Lebo77/Alarm-Clock/Photos/DSC01660.jpg

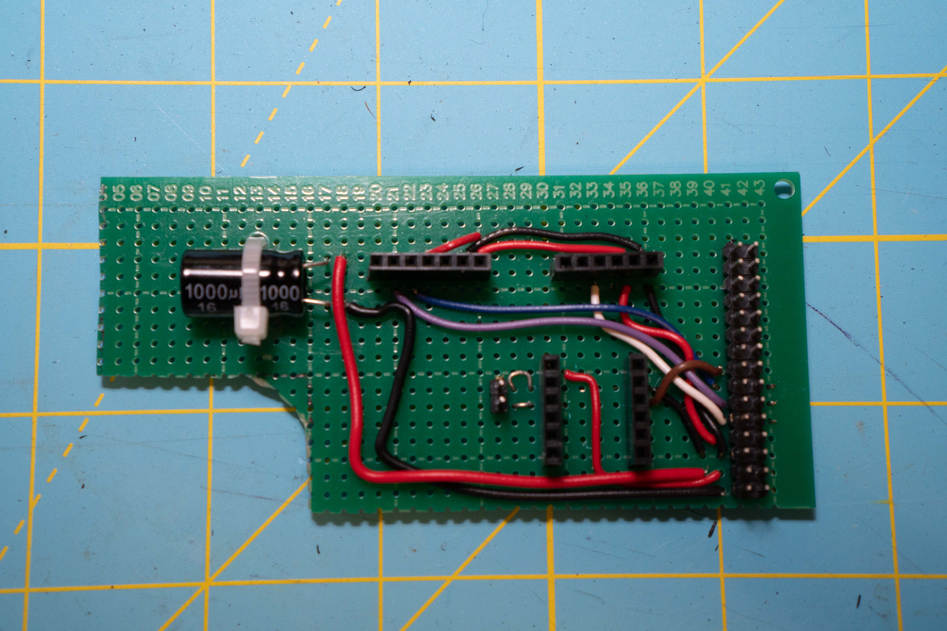
Photos/DSC01660.jpg
