Lebo77/Alarm-Clock/Photos/DSC01661.jpg

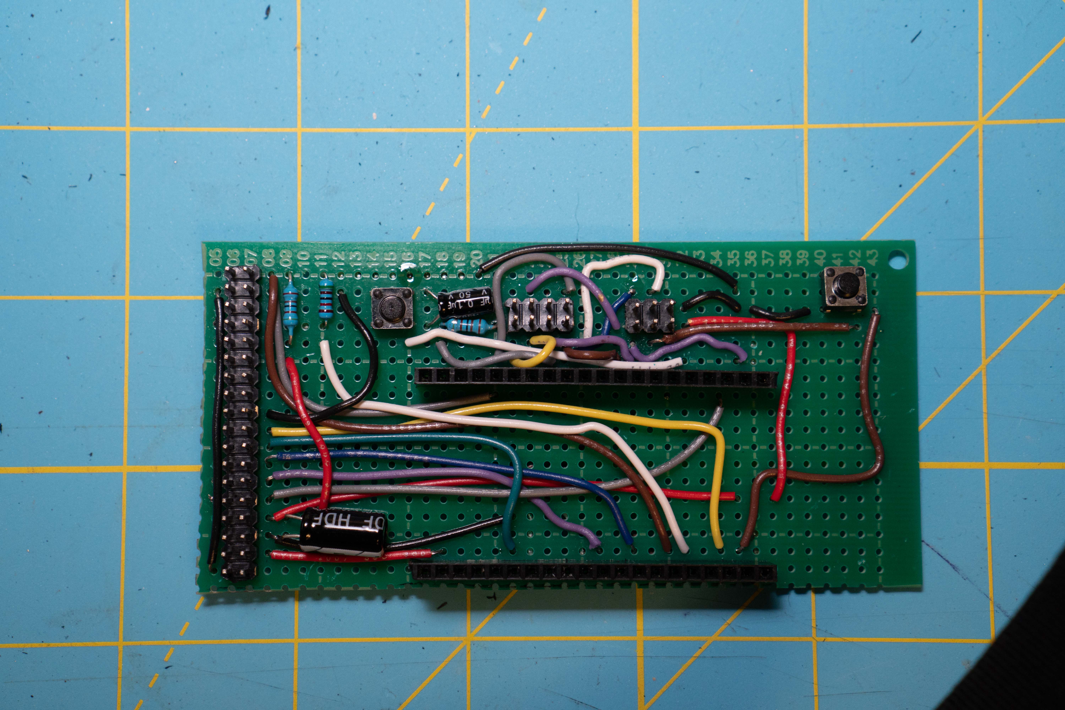
Photos/DSC01661.jpg
