Lebo77/Alarm-Clock/Photos/DSC01662.jpg

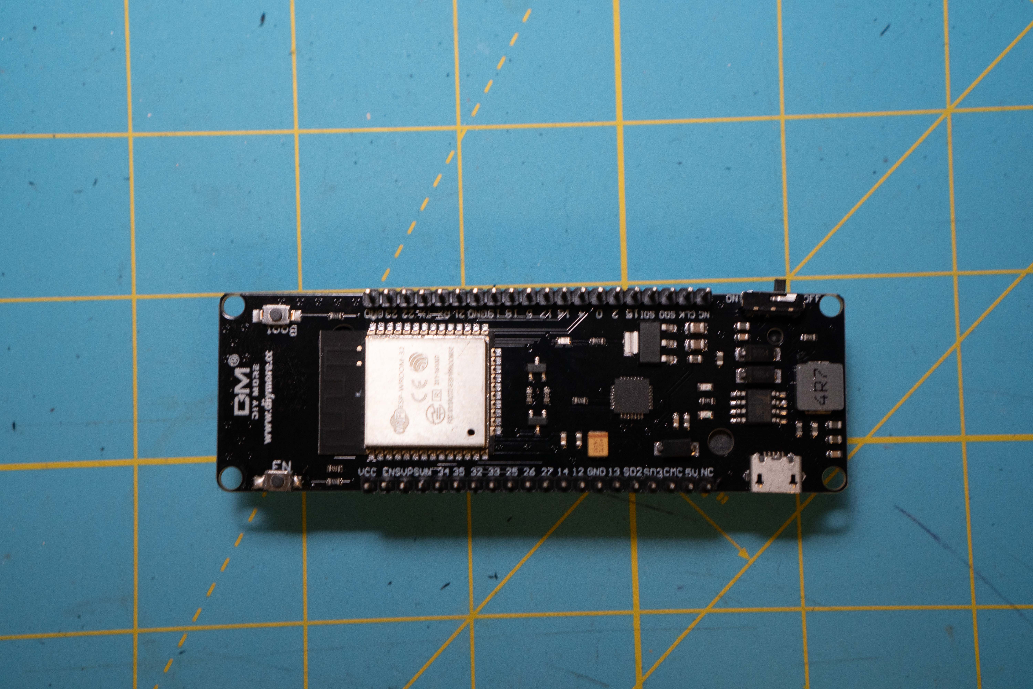
Photos/DSC01662.jpg
