Lebo77/Alarm-Clock/Photos/DSC01663.jpg

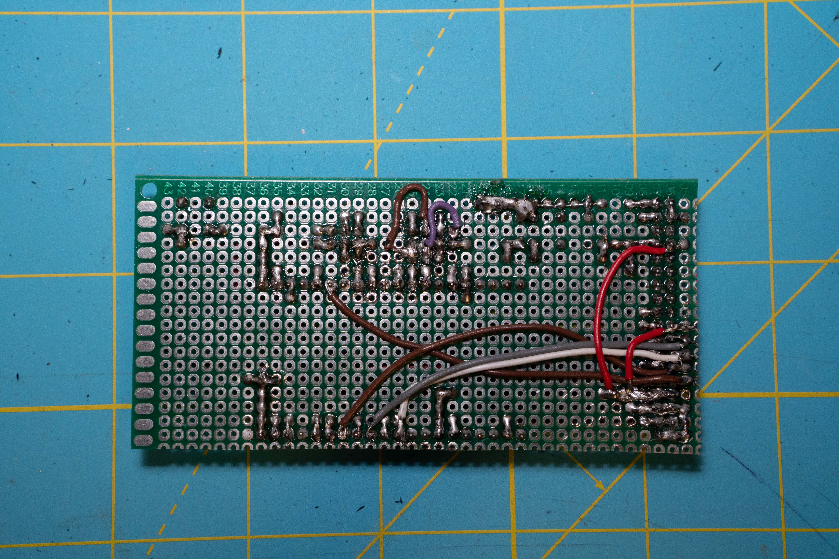
Photos/DSC01663.jpg
