Lebo77/Alarm-Clock/Photos/DSC01664.jpg

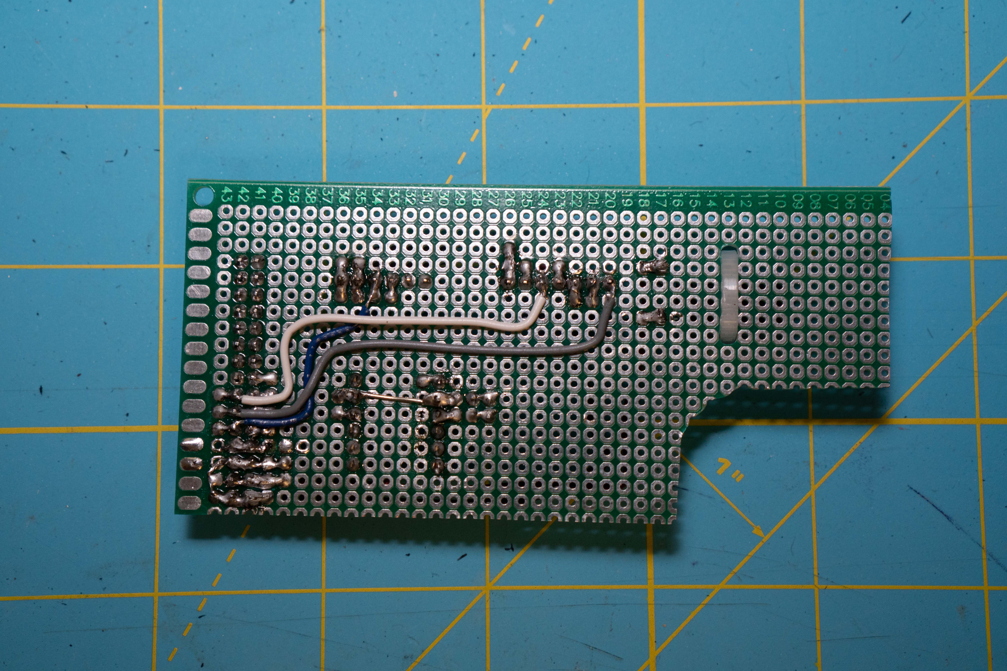
Photos/DSC01664.jpg
