Lebo77/Alarm-Clock/Photos/DSC01665.jpg

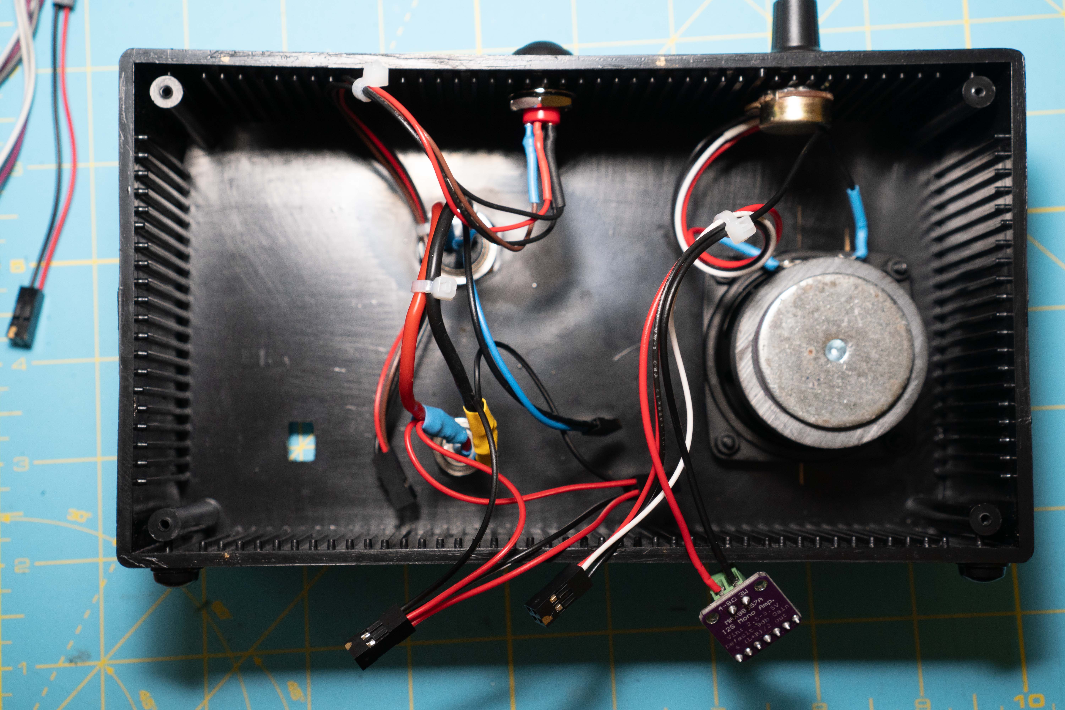
Photos/DSC01665.jpg
