Lebo77/Alarm-Clock/Photos/DSC01667.jpg

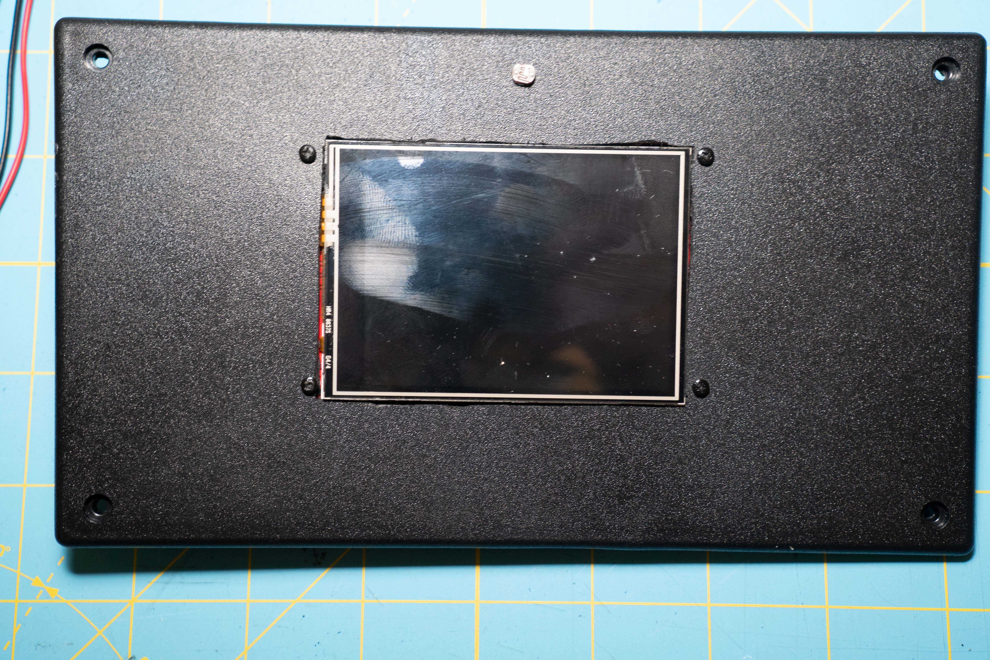
Photos/DSC01667.jpg
