Lebo77/Alarm-Clock/Photos/DSC01668.jpg

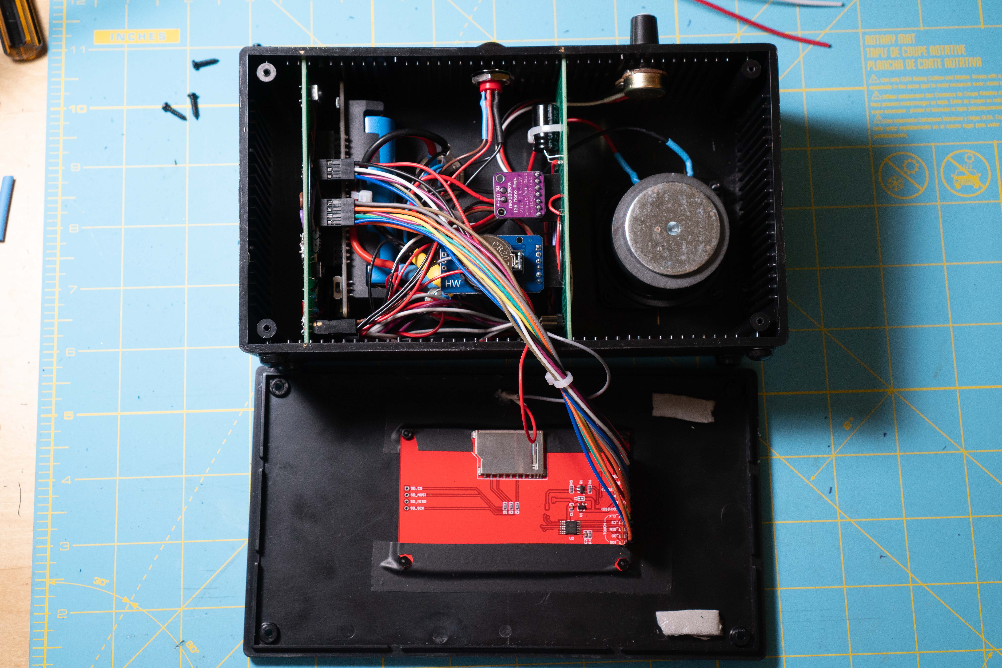
Photos/DSC01668.jpg
