Lebo77/Alarm-Clock/modeMgmt.h

// modeMgmt.h

// mode macros
#define MAIN_MODE             0
#define CURRENT_WX_MODE       1
#define FORECAST_WX_MODE      2
#define HOURLY_WX_MODE        3
#define ALARM_DISPLAY_MODE    4
#define ALARM_SET_MODE        5
#define GEN_LIGHT_CTRL_MODE   6

#define READ_LIGHT_SUB_MODE   0
#define ROOM_LIGHT_SUB_MODE   1
#define NIGHT_LIGHT_SUB_MODE  2
